electgpl/FunctionGenerator/Test/A0001CH1.CSV

Memory Length | 4000
Trigger Level | 0.000E+00
Source | CH1
Probe | 1X
Vertical Units | V
Vertical Scale | 5.000E-01
Vertical Position | 9.800E-01
Horizontal Units | s
Horizontal Scale | 1.000E-03
Horizontal Position | 0.000E+00
Horizontal Mode | Main
Sampling Period | 4.000E-06
Firmware | V1.24
Time
Mode | Fast
Waveform Data
8
8
-5
-6
-7
-6
-6
-7
-7
-7
-8
-7
-9
-8
-8
-9
-9
-9
-10
-10
-11
-10
-11
-11
-11
-11
-12
-12
-12
-13
-12
-12
-12
-13
-13
-14
-14
-15
-15
-15
-15
-15
-16
-17
-16
-16
-16
-17
-17
-17
-17
-17
-17
-18
-19
-19
-18
-18
-19
-18
-20
-20
-20
-20
-20
-19
-19
-20
-21
-21
-19
-21
-21
-21
-21
-22
-22
-21
-22
-22
-22
-22
-22
-22
-22
-22
-23
-22
-22
-23
-23
-23
-24
-23
-23
-22
-23
-24
-23
-23
-23
-23
-23
-23
-23
-24
-23
-24
-23
-24
-23
-25
-24
-23
-23
-24
-24
-24
-24
-24
-22
-24
-25
-24
-24
-24
-24
-23
-24
-24
-24
-24
-24
-24
-23
-24
-25
-23
-24
-24
-24
-23
-25
-24
-24
-23
-24
-24
-23
-25
-25
-24
-23
-24
-24
-23
-23
-24
-24
-23
-24
-25
-24
-24
-24
-24
-23
-24
-24
-23
-23
-23
-23
-22
-24
-22
-22
-22
-23
-22
-22
-22
-23
-22
-22
-21
-22
-22
-22
-21
-21
-21
-21
-21
-22
-21
-20
-20
-20
-20
-20
-19
-18
-19
-19
-19
-18
-19
-18
-18
-18
-18
-17
-16
-17
-16
-16
-16
-16
-16
-16
-14
-15
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
